CShark/usb_dmx/DMX_ArtNet/Inc/config.h

#ifndef __CONFIG_H
#define __CONFIG_H

#include "eth/artnet.h"
#include "lwip/netif.h"

#define ARTNET_NET 0
#define ARTNET_SUB 0
#define ARTNET_UNI 0

#define ARTNET_INPUT 0
#define ARTNET_OUTPUT 1

#pragma pack(4) // 4 Byte alignment for flash storage
typedef enum {
    CONFIGIP_Auto = 0,
    CONFIGIP_Static = 1,
    CONFIGIP_DHCP = 2
} CONFIG_IP_MODE;


typedef struct {
    char ShortName[18];
    char LongName[64];

    char Network;
    char Subnet;
    char Universe;

    char PortDirection;
    ArtNet_Port_Flags PortFlags;
    ArtNet_Failover FailoverMode;
    unsigned char AcnPriority;
} ARTNET_CONFIG;

typedef struct {
    ip_addr_t DhcpServerSelf;
    ip_addr_t DhcpServerClient;
    ip_addr_t DhcpServerSubnet;

    ip_addr_t StaticIp;
    ip_addr_t StaticSubnet;
    ip_addr_t StaticGateway;

    CONFIG_IP_MODE Mode;
    char DhcpServerEnable;

    ARTNET_CONFIG ArtNet[4];
} CONFIG;
#pragma pack()

void Config_Init(struct netif *net, const unsigned char *portDirection);

void Config_Reset();

void Config_SetMode(CONFIG_IP_MODE mode);
void Config_DhcpServer(char enable, ip_addr_t host, ip_addr_t client, ip_addr_t subnet);
void Config_SetIp(const unsigned char *ip);
void Config_SetGateway(const unsigned char *gw);
void Config_SetNetmask(const unsigned char *net);

CONFIG *Config_GetActive();
struct netif* Config_GetNetif();
void Config_ApplyNetwork();
void Config_ApplyArtNet();
void Config_Store();

void Config_StoreFailsafeScene(const unsigned char *buffer, char art_port);
void Config_LoadFailsafeScene(unsigned char* target, int index);


CONFIG Config_GetDefault();


#endif
